smartboxchannel/MODKAM-Flower/PROJECT SOURCE/zstack-lib/commissioning.c

/*********************************************************************
 * INCLUDES
 *********************************************************************/

#include "commissioning.h"
#include "OSAL_PwrMgr.h"
#include "ZDApp.h"
#include "bdb_interface.h"
#include "hal_key.h"
#include "zcl_app.h"

/*********************************************************************
 * LOCAL FUNCTIONS PROTOTYPES
 *********************************************************************/

static void zclCommissioning_ProcessCommissioningStatus(bdbCommissioningModeMsg_t *bdbCommissioningModeMsg);
static void zclCommissioning_ResetBackoffRetry(void);
static void zclCommissioning_BindNotification(bdbBindNotificationData_t *data);
static void zclCommissioning_OnConnect(void);

/*********************************************************************
 * EXTERNAL VARIABLES
 *********************************************************************/

extern bool requestNewTrustCenterLinkKey;
extern bool zclApp_onNet = 0;

/*********************************************************************
 * GLOBAL VARIABLES
 *********************************************************************/

byte rejoinsLeft = APP_COMMISSIONING_END_DEVICE_REJOIN_TRIES;
uint32 rejoinDelay = APP_COMMISSIONING_END_DEVICE_REJOIN_START_DELAY;

uint8 zclCommissioning_TaskId = 0;
#define APP_TX_POWER TX_PWR_PLUS_4

/*********************************************************************
 * @fn      zclCommissioning_Init
 * @brief   Initialize commissioning module
 *********************************************************************/

void zclCommissioning_Init(uint8 task_id)
{
    zclCommissioning_TaskId = task_id;

    // Register callbacks
    bdb_RegisterCommissioningStatusCB(zclCommissioning_ProcessCommissioningStatus);
    bdb_RegisterBindNotificationCB(zclCommissioning_BindNotification);

    // Set transmit power
    ZMacSetTransmitPower(APP_TX_POWER);

    // Important to allow connects through routers
    // To make this work, coordinator should be compiled with this flag: #define TP2_LEGACY_ZC
    requestNewTrustCenterLinkKey = FALSE;
    
#if APP_COMMISSIONING_BY_LONG_PRESS == FALSE
    // Start commissioning automatically
    bdb_StartCommissioning(BDB_COMMISSIONING_MODE_NWK_STEERING | BDB_COMMISSIONING_MODE_FINDING_BINDING);
#else 
    // Wait for long press to start commissioning
    bdb_StartCommissioning(BDB_COMMISSIONING_MODE_IDDLE);
#endif
}

/*********************************************************************
 * @fn      zclCommissioning_ResetBackoffRetry
 * @brief   Reset rejoin backoff parameters
 *********************************************************************/

static void zclCommissioning_ResetBackoffRetry(void)
{
    rejoinsLeft = APP_COMMISSIONING_END_DEVICE_REJOIN_TRIES;
    rejoinDelay = APP_COMMISSIONING_END_DEVICE_REJOIN_START_DELAY;
}

/*********************************************************************
 * @fn      zclCommissioning_OnConnect
 * @brief   Handle successful network connection
 *********************************************************************/

static void zclCommissioning_OnConnect(void)
{
    zclCommissioning_ResetBackoffRetry();
    osal_start_timerEx(zclCommissioning_TaskId, APP_COMMISSIONING_CLOCK_DOWN_POLING_RATE_EVT, 60000);
}

/*********************************************************************
 * @fn      zclCommissioning_ProcessCommissioningStatus
 * @brief   Process BDB commissioning status updates
 *********************************************************************/

static void zclCommissioning_ProcessCommissioningStatus(bdbCommissioningModeMsg_t *bdbCommissioningModeMsg)
{
    switch (bdbCommissioningModeMsg->bdbCommissioningMode) {
    case BDB_COMMISSIONING_INITIALIZATION:
        switch (bdbCommissioningModeMsg->bdbCommissioningStatus) {
        case BDB_COMMISSIONING_NO_NETWORK:
            HAL_TURN_OFF_LED1();
            break;
        case BDB_COMMISSIONING_NETWORK_RESTORED:
            zclCommissioning_OnConnect();
            HAL_TURN_OFF_LED1();
            break;
        default:
            break;
        }
        break;
        
    case BDB_COMMISSIONING_NWK_STEERING:
        switch (bdbCommissioningModeMsg->bdbCommissioningStatus) {
        case BDB_COMMISSIONING_SUCCESS:
            zclCommissioning_OnConnect();
            HAL_TURN_OFF_LED1();
            break;
        default:
            break;
        }
        break;

    case BDB_COMMISSIONING_PARENT_LOST:
        switch (bdbCommissioningModeMsg->bdbCommissioningStatus) {
        case BDB_COMMISSIONING_NETWORK_RESTORED:
            zclCommissioning_ResetBackoffRetry();
            break;

        default:
            // Parent not found, attempt to rejoin again after exponential backoff delay
            if (rejoinsLeft > 0) {
                rejoinDelay = (uint32)((float)rejoinDelay * APP_COMMISSIONING_END_DEVICE_REJOIN_BACKOFF);
                rejoinsLeft -= 1;
            } else {
                rejoinDelay = APP_COMMISSIONING_END_DEVICE_REJOIN_MAX_DELAY;
                zclCommissioning_ResetBackoffRetry();
            }
            osal_start_timerEx(zclCommissioning_TaskId, APP_COMMISSIONING_END_DEVICE_REJOIN_EVT, rejoinDelay);
            break;
        }
        HAL_TURN_OFF_LED1();
        break;
        
    default:
        break;
    }
}

/*********************************************************************
 * @fn      zclCommissioning_ProcessIncomingMsg
 * @brief   Process incoming ZCL messages
 *********************************************************************/

static void zclCommissioning_ProcessIncomingMsg(zclIncomingMsg_t *pInMsg)
{
    if (pInMsg->attrCmd) {
        osal_mem_free(pInMsg->attrCmd);
    }
}

/*********************************************************************
 * @fn      zclCommissioning_Sleep
 * @brief   Configure sleep/polling behavior
 *********************************************************************/

void zclCommissioning_Sleep(uint8 allow)
{
#if defined(POWER_SAVING)
    if (allow) {
        // Enable power saving - set poll rate based on configuration
        if (zclApp_Config.ComparisonPreviousData3 == true) {
            NLME_SetPollRate(6500);   // Poll every 6.5 seconds
        } else {
            NLME_SetPollRate(0);       // Disable polling (deep sleep)
        }
    } else {
        NLME_SetPollRate(POLL_RATE);   // Normal polling rate
    }
#endif
}

/*********************************************************************
 * @fn      zclCommissioning_event_loop
 * @brief   Commissioning event processing loop
 *********************************************************************/

uint16 zclCommissioning_event_loop(uint8 task_id, uint16 events)
{
    if (events & SYS_EVENT_MSG) {
        afIncomingMSGPacket_t *MSGpkt;
        while ((MSGpkt = (afIncomingMSGPacket_t *)osal_msg_receive(zclCommissioning_TaskId))) {

            switch (MSGpkt->hdr.event) {
            case ZDO_STATE_CHANGE:
                // Network state change handled elsewhere
                break;

            case ZCL_INCOMING_MSG:
                zclCommissioning_ProcessIncomingMsg((zclIncomingMsg_t *)MSGpkt);
                break;

            default:
                break;
            }

            // Release the memory
            osal_msg_deallocate((uint8 *)MSGpkt);
        }

        // Return unprocessed events
        return (events ^ SYS_EVENT_MSG);
    }
    
    if (events & APP_COMMISSIONING_END_DEVICE_REJOIN_EVT) {
#if ZG_BUILD_ENDDEVICE_TYPE
        bdb_ZedAttemptRecoverNwk();
        osal_start_timerEx(zclCommissioning_TaskId, APP_COMMISSIONING_CLOCK_DOWN_POLING_RATE_EVT, 60000);
#endif
        return (events ^ APP_COMMISSIONING_END_DEVICE_REJOIN_EVT);
    }

    if (events & APP_COMMISSIONING_CLOCK_DOWN_POLING_RATE_EVT) {
        zclCommissioning_Sleep(true);
        return (events ^ APP_COMMISSIONING_CLOCK_DOWN_POLING_RATE_EVT);
    }
    
#if APP_COMMISSIONING_BY_LONG_PRESS == TRUE    
    if (events & APP_COMMISSIONING_BY_LONG_PRESS_EVT) {
        HAL_TURN_ON_LED1();
        osal_start_timerEx(zclCommissioning_TaskId, APP_COMMISSIONING_OFF_EVT, 14000);
        bdb_StartCommissioning(BDB_COMMISSIONING_MODE_NWK_STEERING | BDB_COMMISSIONING_MODE_FINDING_BINDING);
        sendInitReportCount = 0;
        return (events ^ APP_COMMISSIONING_BY_LONG_PRESS_EVT);
    }
    
    if (events & APP_COMMISSIONING_OFF_EVT) {
        HAL_TURN_OFF_LED1();
        // bdb_StartCommissioning(BDB_COMMISSIONING_MODE_IDDLE);
        return (events ^ APP_COMMISSIONING_OFF_EVT);
    }
#endif
    
    // Discard unknown events
    return 0;
}

/*********************************************************************
 * @fn      zclCommissioning_BindNotification
 * @brief   Handle binding notifications
 *********************************************************************/

static void zclCommissioning_BindNotification(bdbBindNotificationData_t *data)
{
    uint16 maxEntries = 0, usedEntries = 0;
    bindCapacity(&maxEntries, &usedEntries);
}

/*********************************************************************
 * @fn      zclCommissioning_HandleKeys
 * @brief   Handle key presses for commissioning
 *********************************************************************/

void zclCommissioning_HandleKeys(uint8 portAndAction, uint8 keyCode)
{
    if (portAndAction & HAL_KEY_PRESS) {
#if ZG_BUILD_ENDDEVICE_TYPE
        if (devState == DEV_NWK_ORPHAN) {
            bdb_ZedAttemptRecoverNwk();
        }
#endif
    }
    
#if APP_COMMISSIONING_BY_LONG_PRESS == TRUE 
    if (portAndAction & HAL_KEY_RELEASE) {
        // Cancel long press timer on key release
        osal_stop_timerEx(zclCommissioning_TaskId, APP_COMMISSIONING_BY_LONG_PRESS_EVT);
    } else {
        bool statTimer = true;
#if APP_COMMISSIONING_BY_LONG_PRESS_PORT
        statTimer = APP_COMMISSIONING_BY_LONG_PRESS_PORT & portAndAction;
#endif
        // Start long press timer if not on network
        if (statTimer && bdbAttributes.bdbNodeIsOnANetwork == 0) {
            uint32 timeout = APP_COMMISSIONING_HOLD_TIME_FAST;
            osal_start_timerEx(zclCommissioning_TaskId, APP_COMMISSIONING_BY_LONG_PRESS_EVT, timeout);
        }
    }
#endif    
}
