smartboxchannel/MODKAM-Flower/PROJECT SOURCE/zstack-lib/hal_key.h

/**************************************************************************************************
  Filename:       hal_key.h
  Revised:        $Date: 2007-07-06 10:42:24 -0700 (Fri, 06 Jul 2007) $
  Revision:       $Revision: 13579 $

  Description:    This file contains the interface to the KEY Service.

  Copyright 2005-2012 Texas Instruments Incorporated. All rights reserved.

  IMPORTANT: Your use of this Software is limited to those specific rights
  granted under the terms of a software license agreement between the user
  who downloaded the software, his/her employer (which must be your employer)
  and Texas Instruments Incorporated (the "License").  You may not use this
  Software unless you agree to abide by the terms of the License. The License
  limits your use, and you acknowledge, that the Software may not be modified,
  copied or distributed unless embedded on a Texas Instruments microcontroller
  or used solely and exclusively in conjunction with a Texas Instruments radio
  frequency transceiver, which is integrated into your product.  Other than for
  the foregoing purpose, you may not use, reproduce, copy, prepare derivative
  works of, modify, distribute, perform, display or sell this Software and/or
  its documentation for any purpose.

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
  Should you have any questions regarding your right to use this Software,
  contact Texas Instruments Incorporated at www.TI.com. 
**************************************************************************************************/

#ifndef HAL_KEY_H
#define HAL_KEY_H

#ifdef __cplusplus
extern "C"
{
#endif

/**************************************************************************************************
 * INCLUDES
 **************************************************************************************************/
#include "hal_board.h"
  
/**************************************************************************************************
 * CONSTANTS
 **************************************************************************************************/

// Bit masks
#define HAL_KEY_BIT0   0x01
#define HAL_KEY_BIT1   0x02
#define HAL_KEY_BIT2   0x04
#define HAL_KEY_BIT3   0x08
#define HAL_KEY_BIT4   0x10
#define HAL_KEY_BIT5   0x20
#define HAL_KEY_BIT6   0x40
#define HAL_KEY_BIT7   0x80

// Interrupt option
#define HAL_KEY_INTERRUPT_DISABLE    0x00
#define HAL_KEY_INTERRUPT_ENABLE     0x01

// Key state
#define HAL_KEY_STATE_NORMAL          0x00
#define HAL_KEY_STATE_SHIFT           0x01

// Edge detection
#define HAL_KEY_RISING_EDGE  0
#define HAL_KEY_FALLING_EDGE 1

// Port definitions
#define HAL_KEY_PORT0 0x01
#define HAL_KEY_PORT1 0x02
#define HAL_KEY_PORT2 0x04

// Key event types
#define HAL_KEY_PRESS   0x20
#define HAL_KEY_RELEASE 0x40

// Button definitions
#define HAL_KEY_SW_1 0x01  // Joystick up
#define HAL_KEY_SW_2 0x02  // Joystick right
#define HAL_KEY_SW_5 0x04  // Joystick center
#define HAL_KEY_SW_4 0x08  // Joystick left
#define HAL_KEY_SW_3 0x10  // Joystick down

#define HAL_KEY_SW_6 0x20  // Button S1 if available
#define HAL_KEY_SW_7 0x40  // Button S2 if available

/**************************************************************************************************
 * TYPEDEFS
 **************************************************************************************************/
typedef void (*halKeyCBack_t)(uint8 keys, uint8 state);

/**************************************************************************************************
 * GLOBAL VARIABLES
 **************************************************************************************************/
extern bool Hal_KeyIntEnable;

/**************************************************************************************************
 * FUNCTION PROTOTYPES - API
 **************************************************************************************************/

/*
 * Initialize the Key Service
 */
extern void HalKeyInit(void);

/*
 * Configure the Key Service
 */
extern void HalKeyConfig(bool interruptEnable, const halKeyCBack_t cback);

/*
 * Read the Key status
 */
extern uint8 HalKeyRead(void);

/*
 * Enter sleep mode, store important values
 */
extern void HalKeyEnterSleep(void);

/*
 * Exit sleep mode, restore values
 */
extern uint8 HalKeyExitSleep(void);

/*
 * This is for internal use by hal_driver
 */
extern void HalKeyPoll(void);

/*
 * This is for internal use by hal_sleep
 */
extern bool HalKeyPressed(void);

extern uint8 hal_key_keys(void);
extern uint8 hal_key_int_keys(void);

#ifdef __cplusplus
}
#endif

#endif /* HAL_KEY_H */
