smartboxchannel/MODKAM-Flower/PROJECT SOURCE/Source/stdint.h

#ifndef _STDINT
#define _STDINT

/*********************************************************************
 * INTEGER TYPE DEFINITIONS
 * Map standard C types to compiler-specific types
 *********************************************************************/

#ifndef int8_t
    #define int8_t  int8
#endif
#ifndef int16_t
    #define int16_t int16
#endif
#ifndef int32_t
    #define int32_t int32
#endif
#ifndef int64_t
    #define int64_t int64
#endif
#ifndef uint8_t
    #define uint8_t  uint8
#endif
#ifndef uint16_t
    #define uint16_t uint16
#endif
#ifndef uint32_t
    #define uint32_t uint32
#endif

/*********************************************************************
 * CONSTANT MACROS
 *********************************************************************/

#define S8_C(x)  x
#define U8_C(x)  x
#define S16_C(x) x
#define U16_C(x) x
#define S32_C(x) x
#define U32_C(x) x
#define S64_C(x) x
#define U64_C(x) x

#endif /* _STDINT */
