smartboxchannel/MODKAM-Flower/PROJECT SOURCE/zstack-lib/Debug.h

#ifndef _DEBUG_H
#define _DEBUG_H

/*********************************************************************
 * INCLUDES
 *********************************************************************/

#include "hal_types.h"
#include "hal_uart.h"
#include <stdarg.h>
#include <stdio.h>
#include <string.h>

/*********************************************************************
 * CONSTANTS
 *********************************************************************/

#define BUFFLEN 128
#define BUFFER 100

#define PRINT_NUMBER_TYPE long

#define PAD_RIGHT 1
#define PAD_ZERO 2

#define PRINT_BUF_LEN 12

#define PRINT_IMMEDIATE_PRINT 0

/*********************************************************************
 * MACROS
 *********************************************************************/

// Macro to print a byte in binary format
#define BYTE_TO_BINARY_PATTERN "%c%c%c%c%c%c%c%c"
#define BYTE_TO_BINARY(byte)  \
  (byte & 0x80 ? '1' : '0'), \
  (byte & 0x40 ? '1' : '0'), \
  (byte & 0x20 ? '1' : '0'), \
  (byte & 0x10 ? '1' : '0'), \
  (byte & 0x08 ? '1' : '0'), \
  (byte & 0x04 ? '1' : '0'), \
  (byte & 0x02 ? '1' : '0'), \
  (byte & 0x01 ? '1' : '0')

/*********************************************************************
 * EXTERNAL VARIABLES
 *********************************************************************/

extern halUARTCfg_t halUARTConfig;

/*********************************************************************
 * FUNCTION PROTOTYPES
 *********************************************************************/

void vprint(const char *fmt, va_list argp);
extern bool DebugInit(void);
extern void LREP(char *format, ...);
extern void LREPMaster(uint8 *data);

#endif /* _DEBUG_H */
