smartboxchannel/MODKAM-Flower/PROJECT SOURCE/zstack-lib/delay.h

#ifndef DELAY_H
#define DELAY_H

/*********************************************************************
 * FUNCTION PROTOTYPES
 *********************************************************************/

extern void delay_us(uint16 microSecs);
extern void delay_ms(uint16 milliSecs);

#endif /* DELAY_H */
