smartboxchannel/MODKAM-Flower/PROJECT SOURCE/zstack-lib/utils.c

/*********************************************************************
 * INCLUDES
 *********************************************************************/

#include "utils.h"
#include "hal_adc.h"

/*********************************************************************
 * @fn      mapRange
 * @brief   Maps a value from one range to another and clamps the result
 *********************************************************************/

double mapRange(double a1, double a2, double b1, double b2, double s)
{
    double result = b1 + (s - a1) * (b2 - b1) / (a2 - a1);
    return MIN(b2, MAX(result, b1));
}

/*********************************************************************
 * @fn      adcReadSampled
 * @brief   Reads ADC multiple times and returns average value
 *********************************************************************/

uint16 adcReadSampled(uint8 channel, uint8 resolution, uint8 reference, uint8 samplesCount)
{
    HalAdcSetReference(reference);
    uint32 samplesSum = 0;
    
    for (uint8 i = 0; i < samplesCount; i++) {
        samplesSum += HalAdcRead(channel, resolution);
    }
    
    return samplesSum / samplesCount;
}
